simonschimik/Messung-von-Raumklimadaten-mittels-IoT-Technik-in-Bezug-auf-die-Uebertragung-von-SARS-CoV-2/Final-Arduino/doc/html/_data_logging_handler_8cpp__incl.png

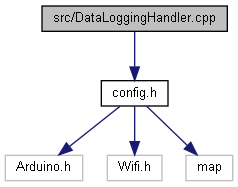
Final-Arduino/doc/html/_data_logging_handler_8cpp__incl.png
