simonschimik/Messung-von-Raumklimadaten-mittels-IoT-Technik-in-Bezug-auf-die-Uebertragung-von-SARS-CoV-2/Final-Arduino/doc/html/config_8h__dep__incl.png

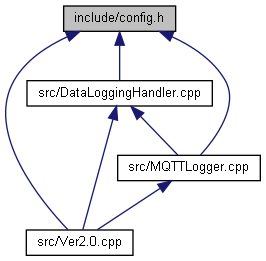
Final-Arduino/doc/html/config_8h__dep__incl.png
