simonschimik/Messung-von-Raumklimadaten-mittels-IoT-Technik-in-Bezug-auf-die-Uebertragung-von-SARS-CoV-2/Final-Arduino/doc/html/d0/d9b/_ver2_80_8cpp_a0ae472404ee7e7f966698ca3652a637d_icgraph.png

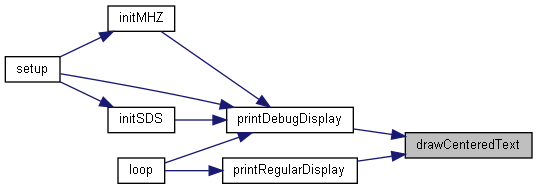
Final-Arduino/doc/html/d0/d9b/_ver2_80_8cpp_a0ae472404ee7e7f966698ca3652a637d_icgraph.png
