simonschimik/Messung-von-Raumklimadaten-mittels-IoT-Technik-in-Bezug-auf-die-Uebertragung-von-SARS-CoV-2/Final-Arduino/doc/html/d0/d9b/_ver2_80_8cpp_a4fc01d736fe50cf5b977f755b675f11d_cgraph.png

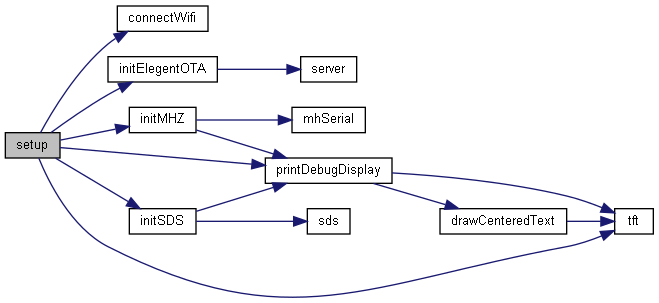
Final-Arduino/doc/html/d0/d9b/_ver2_80_8cpp_a4fc01d736fe50cf5b977f755b675f11d_cgraph.png
