simonschimik/Messung-von-Raumklimadaten-mittels-IoT-Technik-in-Bezug-auf-die-Uebertragung-von-SARS-CoV-2/Final-Arduino/doc/html/d0/d9b/_ver2_80_8cpp_a5ea9d967ee330c0e32716b0892d2be3d_icgraph.png

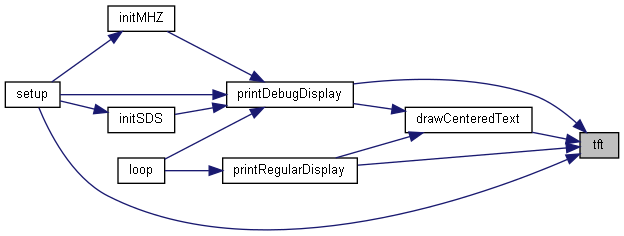
Final-Arduino/doc/html/d0/d9b/_ver2_80_8cpp_a5ea9d967ee330c0e32716b0892d2be3d_icgraph.png
