simonschimik/Messung-von-Raumklimadaten-mittels-IoT-Technik-in-Bezug-auf-die-Uebertragung-von-SARS-CoV-2/Final-Arduino/doc/html/d0/d9b/_ver2_80_8cpp_a09b58885fef1104f63acb80539f9dd88_icgraph.png

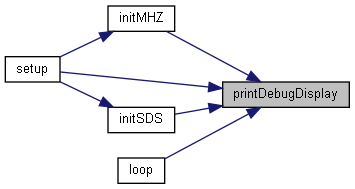
Final-Arduino/doc/html/d0/d9b/_ver2_80_8cpp_a09b58885fef1104f63acb80539f9dd88_icgraph.png
