simonschimik/Messung-von-Raumklimadaten-mittels-IoT-Technik-in-Bezug-auf-die-Uebertragung-von-SARS-CoV-2/Final-Arduino/doc/html/d0/d9b/_ver2_80_8cpp_a454400cf140d9c48bdcaf735995a72fd_cgraph.png

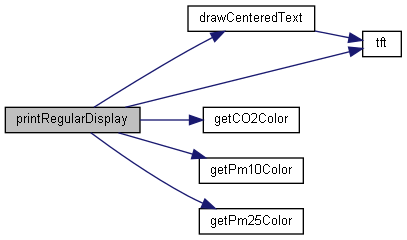
Final-Arduino/doc/html/d0/d9b/_ver2_80_8cpp_a454400cf140d9c48bdcaf735995a72fd_cgraph.png
