simonschimik/Messung-von-Raumklimadaten-mittels-IoT-Technik-in-Bezug-auf-die-Uebertragung-von-SARS-CoV-2/Final-Arduino/doc/html/d0/d9b/_ver2_80_8cpp_afe461d27b9c48d5921c00d521181f12f_cgraph.png

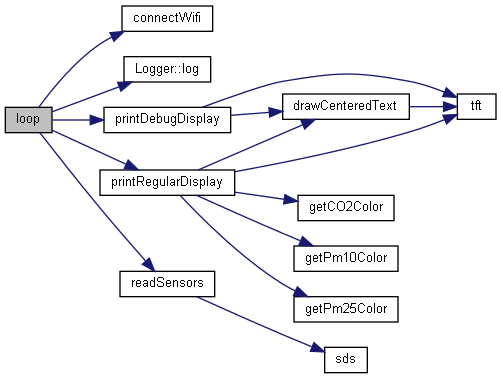
Final-Arduino/doc/html/d0/d9b/_ver2_80_8cpp_afe461d27b9c48d5921c00d521181f12f_cgraph.png
