simonschimik/Messung-von-Raumklimadaten-mittels-IoT-Technik-in-Bezug-auf-die-Uebertragung-von-SARS-CoV-2/Final-Arduino/doc/html/d0/ddd/_ver2_80_8cpp__incl.png

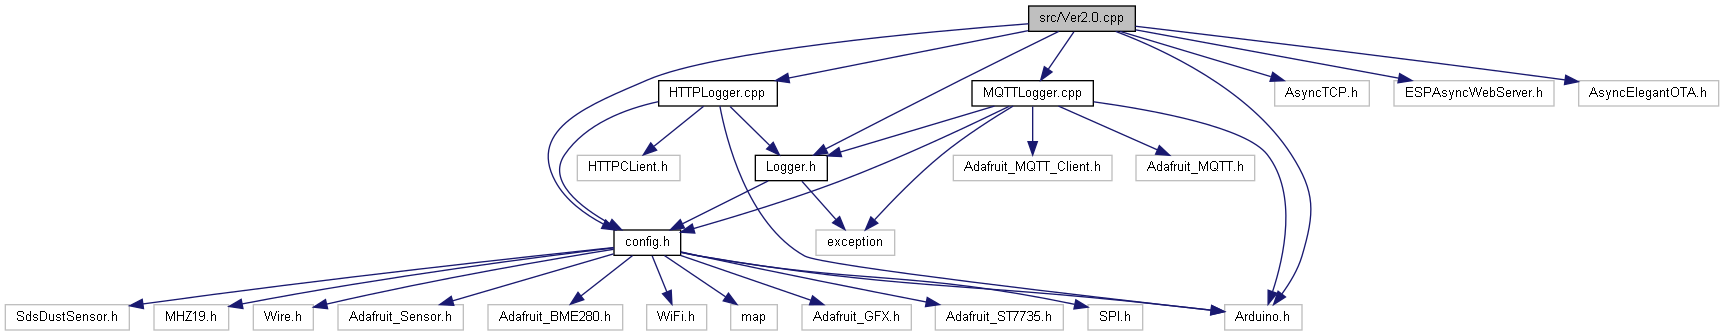
Final-Arduino/doc/html/d0/ddd/_ver2_80_8cpp__incl.png
