simonschimik/Messung-von-Raumklimadaten-mittels-IoT-Technik-in-Bezug-auf-die-Uebertragung-von-SARS-CoV-2/Final-Arduino/doc/html/d0/df4/_h_t_t_p_logger_8cpp__incl.png

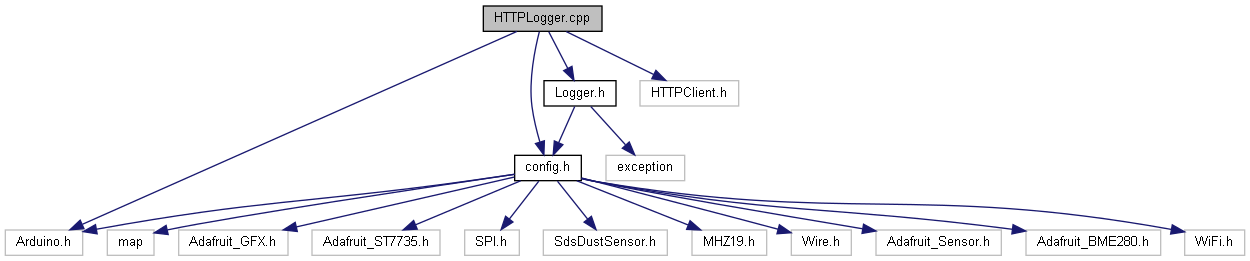
Final-Arduino/doc/html/d0/df4/_h_t_t_p_logger_8cpp__incl.png
