simonschimik/Messung-von-Raumklimadaten-mittels-IoT-Technik-in-Bezug-auf-die-Uebertragung-von-SARS-CoV-2/Final-Arduino/doc/html/d2/d22/_logger_8h__dep__incl.png

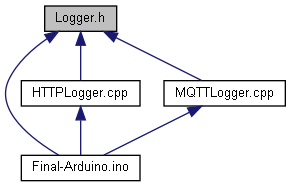
Final-Arduino/doc/html/d2/d22/_logger_8h__dep__incl.png
