simonschimik/Messung-von-Raumklimadaten-mittels-IoT-Technik-in-Bezug-auf-die-Uebertragung-von-SARS-CoV-2/Final-Arduino/doc/html/d3/d9b/_m_q_t_t_logger_8cpp__incl.png

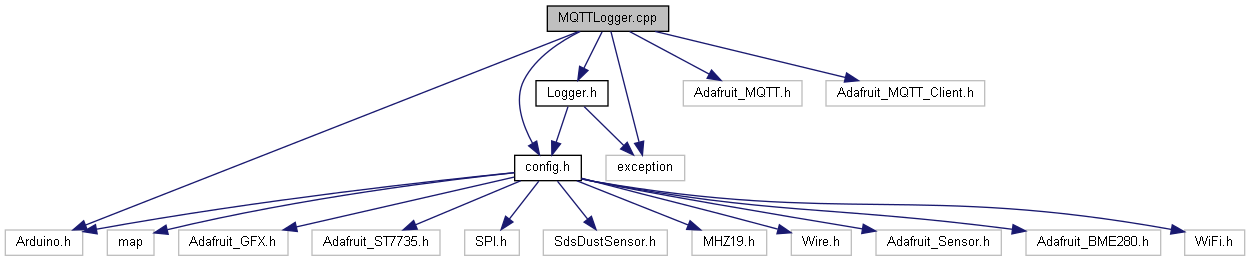
Final-Arduino/doc/html/d3/d9b/_m_q_t_t_logger_8cpp__incl.png
