simonschimik/Messung-von-Raumklimadaten-mittels-IoT-Technik-in-Bezug-auf-die-Uebertragung-von-SARS-CoV-2/Components/SDS011/SDS011.ino

#include <SdsDustSensor.h>

int rxPin = 25;
int txPin = 26;
SdsDustSensor sds(rxPin, txPin);

void setup() {
  Serial.begin(9600);
  sds.begin();

  Serial.println(sds.queryFirmwareVersion().toString()); // prints firmware version
  Serial.println(sds.setQueryReportingMode().toString()); // ensures sensor is in 'query' reporting mode
}

void loop() {
  sds.wakeup();
  delay(2000);

  PmResult pm = sds.queryPm();
  if (pm.isOk()) {
    Serial.print("PM2.5 = ");
    Serial.print(pm.pm25);
    Serial.print(", PM10 = ");
    Serial.println(pm.pm10);
  } else {
    Serial.print("Could not read values from sensor, reason: ");
    Serial.println(pm.statusToString());
  }

}
