simonschimik/Messung-von-Raumklimadaten-mittels-IoT-Technik-in-Bezug-auf-die-Uebertragung-von-SARS-CoV-2/Components/TFT/TFT.ino

#include <Adafruit_GFX.h>    // Core graphics library
#include <Adafruit_ST7735.h> // Hardware-specific library for ST7735
#include <SPI.h>

#define TFT_CS         5 
#define TFT_RST        17                                
#define TFT_DC         16 

Adafruit_ST7735 tft = Adafruit_ST7735(TFT_CS, TFT_DC, TFT_RST);

void setup() {
  Serial.begin(9600);

  tft.initR(INITR_BLACKTAB); 
  tft.fillScreen(ST7735_BLACK);
  tft.setCursor(0, 0);
  tft.setTextColor(ST7735_WHITE);
  tft.setTextWrap(true);
  tft.print("Hello World!");
}

void loop(){

}
